VialeJ/Chargeur-Batterie/Thomas F/Compte Rendu/Compte Rendu - 03-02-2025.pdf

Compte Rendu de fin de séance
Thomas Faucherre
03/02/2025 :
Durant cette séance, j’ai réalisé le schéma du DS6521.
Nous avons un DS65211FF8, soit une pièce adaptée pour une tension de batterie de 4.2V, avec une Thermistance entre 0 et 45°C en package ESOP-8L.
Voici le schéma réalisé sur EasyEDA :

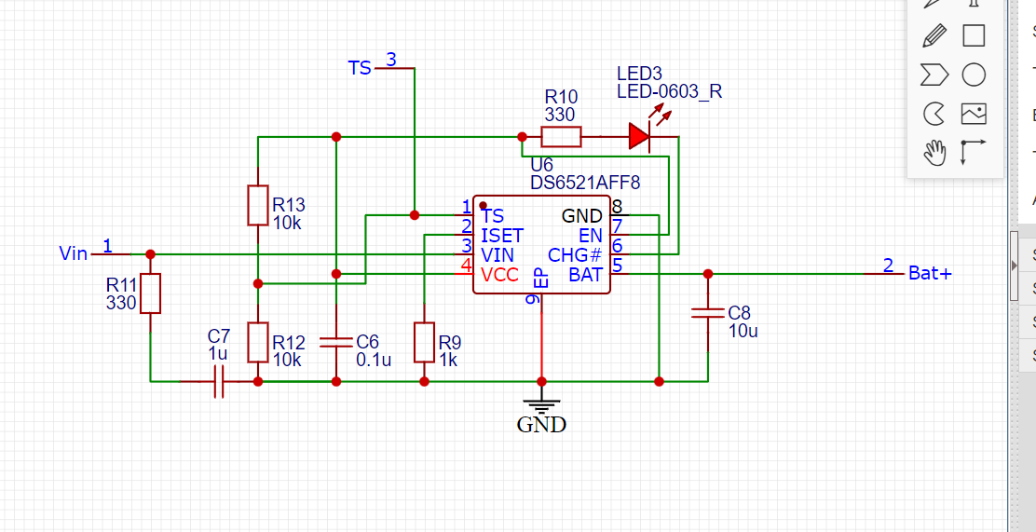
[picture p30: figure]

En accord avec notre CDC, Vin peut monter jusqu’à 28V. De ce fait nous allons placer la LED indicatrice de charge sur VCC qui est un régulateur interne de 5V, avec une résistance de 330 ohms de manière à limiter le courant. Les condensateurs aux bornes de Vin, Vcc et Vbat permettent de lisser la tension et de prévenir les forts appels de courant.
ISET est relié à une résistance de 1k pour permettre de charger notre cellule à 1A, en accord avec la datasheet :

Soit avec la table de valeurs caractéristiques du système : Viset = 1 V. Donc :

Cette valeur nous permet d’obtenir un courant de charge de 1A.
Nous avons également besoin de dimensionner le système autour de la résistance RTS et RBOT :

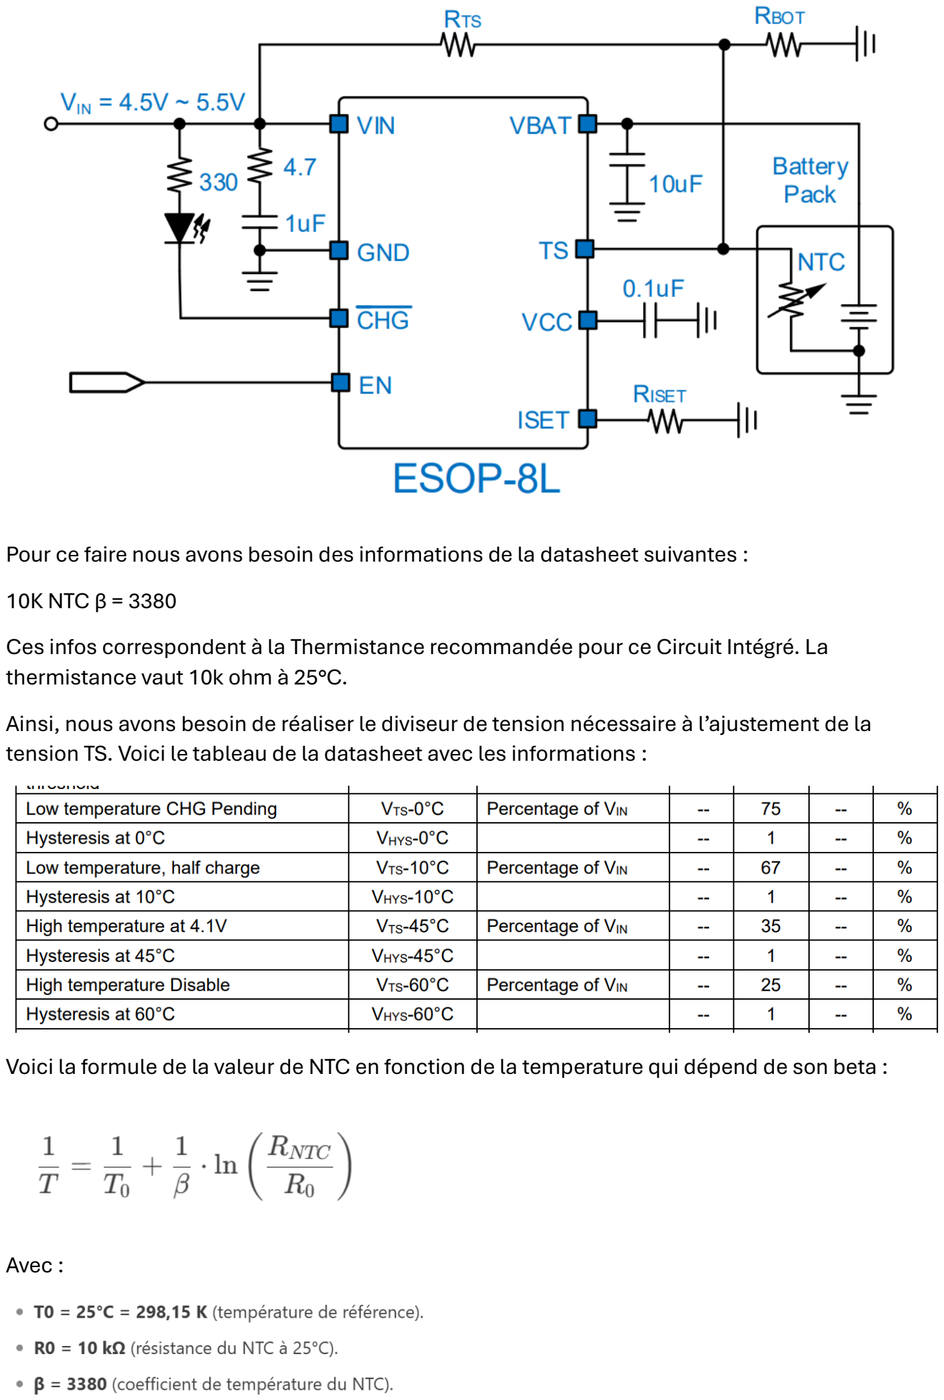
[picture p31: page 2]

Pour ce faire nous avons besoin des informations de la datasheet suivantes :
10K NTC β = 3380
Ces infos correspondent à la Thermistance recommandée pour ce Circuit Intégré. La thermistance vaut 10k ohm à 25°C.
Ainsi, nous avons besoin de réaliser le diviseur de tension nécessaire à l’ajustement de la tension TS. Voici le tableau de la datasheet avec les informations :

Voici la formule de la valeur de NTC en fonction de la temperature qui dépend de son beta :

Avec :

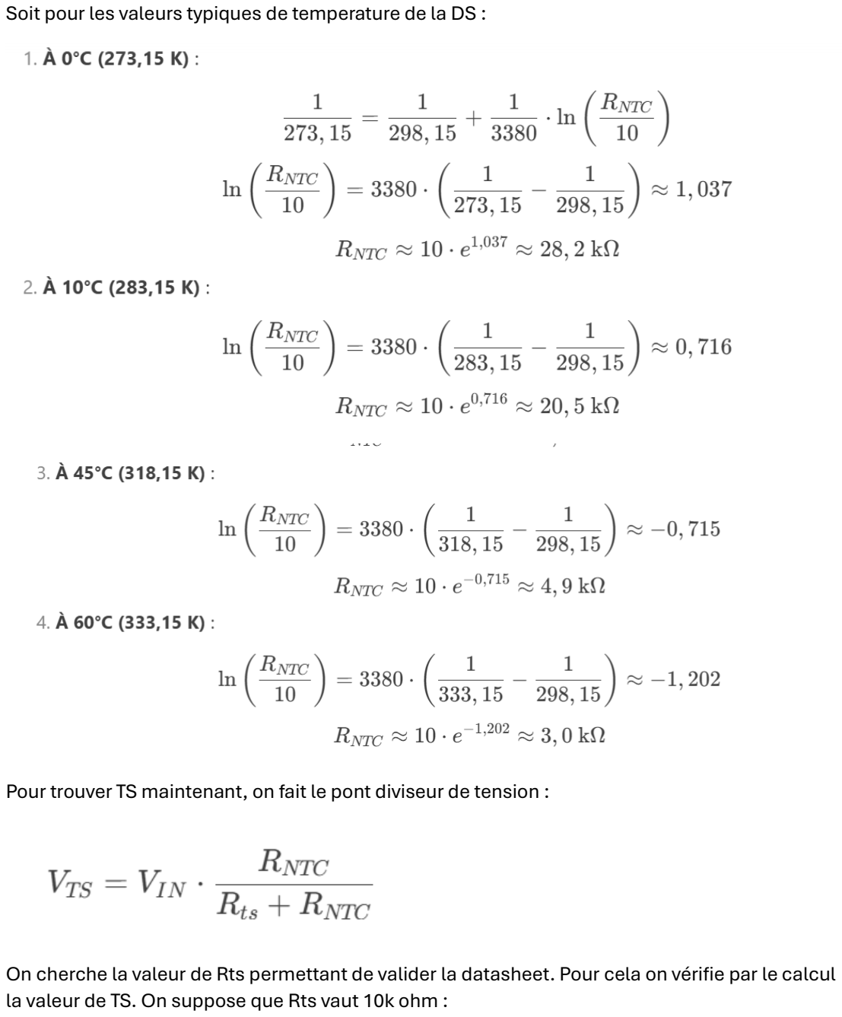
[picture p32: page 3]

Soit pour les valeurs typiques de temperature de la DS :

Pour trouver TS maintenant, on fait le pont diviseur de tension :

On cherche la valeur de Rts permettant de valider la datasheet. Pour cela on vérifie par le calcul la valeur de TS. On suppose que Rts vaut 10k ohm :

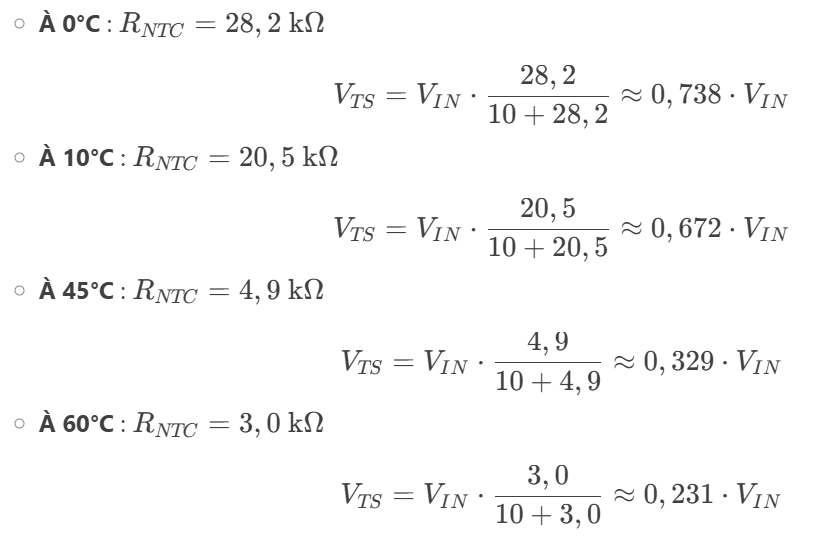
[picture p33: figure]

On constate que les valeurs obtenues concordent avec la datasheet, on peut en déduire que RTS vaut bien 10k ohm.
Pour ce qui est de RBOT, on prendra la même valeur que la NTC.
